ukayzm/dwr/proto1/test/motor_direction/README.md

# Test Motor Direction

It loops with these actions:
* Two motors rotate forward for 1 second in max speed
* Two motors pause for 1 second
* Two motors rotate backward for 1 second in max speed
* Two motors stop for 3 second

The followings can be tested:
* wire connections
* direction of motor and wheel. Switch dirA and dirB if the rotation direction is in reverse.
