ukayzm/dwr/proto1/sketch/motor.h

#ifndef __MOTOR_H__
#define __MOTOR_H__


#include <inttypes.h>


class Motor
{
public:
	void setRpm(int16_t rpm) {
		tgtRpm = rpm;
	}
	int16_t getAccelRpm(void) {
		return curRpm - prevRpm;
	}
	int16_t getCurRpm(void) {
		return curRpm;
	}
	int16_t getMaxRpm(void) {
		return maxRpm;
	}
	void incRpmPercent(int percent_point)
	{
		int16_t new_rpm = tgtRpm + (long)maxRpm * percent_point / 100;
		if (new_rpm >= maxRpm) {
			new_rpm = maxRpm;
		} else if (new_rpm <= -maxRpm) {
			new_rpm = -maxRpm;
		}
		setRpm(new_rpm);
	}
	virtual void loop(void);
	int id;
protected:
	int16_t maxRpm, tgtRpm;
	int16_t prevRpm, curRpm;
};


#endif // __MOTOR_H__
