ukayzm/dwr/tests/hc05_data/hc05_data.ino

#include <SoftwareSerial.h>

SoftwareSerial BTserial(A0, A1); // RX | TX
const long baudRate = 115200;

#define MAX_CHAR	128
char line_buf[MAX_CHAR];
int buf_len = 0;

void setup() 
{
	Serial.begin(115200);
	Serial.print("Sketch:   ");   Serial.println(__FILE__);
	Serial.print("Uploaded: ");   Serial.println(__DATE__);

	BTserial.begin(baudRate);  
	Serial.print("BTserial started at "); Serial.println(baudRate);
	Serial.print("> ");
}

void loop()
{
	// Read from the Bluetooth module and send to the Arduino Serial Monitor
	if (BTserial.available()) {
		char c = BTserial.read();
		Serial.write(c);
		if (c == '\n') {
			Serial.write("> ");
		}
	}

	// Read from the Serial Monitor and send to the Bluetooth module
	if (Serial.available()) {
		char c = Serial.read();
		if (buf_len < MAX_CHAR) {
			line_buf[buf_len++] = c;
		}
		Serial.write(c);
		if (buf_len == MAX_CHAR || c == '\n') {
			unsigned long start_usec = micros();
			for (int i = 0; i < buf_len; i++) {
				BTserial.write(line_buf[i]);   
			}
			unsigned long cur_usec = micros();
			Serial.print(buf_len);
			Serial.print(F(" chars sent in "));
			Serial.print(cur_usec - start_usec);
			Serial.println(F(" usec"));
			buf_len = 0;
		}
	}
}
