ukayzm/dwr/proto3/test/dc-motor/main/motor_test.h

#ifndef __MOTOR_TEST_H__
#define __MOTOR_TEST_H__

#include "motor.h"

extern void do_motor_test1(Motor *m0, Motor *m1);
extern void do_motor_test_pwm(Motor *m0, Motor *m1);
extern void do_motor_test2(Motor *m0, Motor *m1);
extern void do_motor_test3(Motor *m0, Motor *m1);
extern void do_motor_test4(Motor *m);

#endif // __MOTOR_TEST_H__
