ukayzm/dwr/proto1/test/mpu6050/mpu6050_dmp6.cpp

/*
 * This code is taken from https://github.com/jrowberg/i2cdevlib.
 * DMP is used without interrupt.
 */

// I2C device class (I2Cdev) demonstration Arduino sketch for MPU6050 class using DMP (MotionApps v2.0)
// 6/21/2012 by Jeff Rowberg <jeff@rowberg.net>
// Updates should (hopefully) always be available at https://github.com/jrowberg/i2cdevlib
//

/* ============================================
I2Cdev device library code is placed under the MIT license
Copyright (c) 2012 Jeff Rowberg

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
THE SOFTWARE IS PROVIDED "AS IS", WITHOUT WARRANTY OF ANY KIND, EXPRESS OR
IMPLIED, INCLUDING BUT NOT LIMITED TO THE WARRANTIES OF MERCHANTABILITY,
FITNESS FOR A PARTICULAR PURPOSE AND NONINFRINGEMENT. IN NO EVENT SHALL THE
AUTHORS OR COPYRIGHT HOLDERS BE LIABLE FOR ANY CLAIM, DAMAGES OR OTHER
LIABILITY, WHETHER IN AN ACTION OF CONTRACT, TORT OR OTHERWISE, ARISING FROM,
OUT OF OR IN CONNECTION WITH THE SOFTWARE OR THE USE OR OTHER DEALINGS IN
THE SOFTWARE.
===============================================
*/

// I2Cdev and MPU6050 must be installed as libraries, or else the .cpp/.h files
// for both classes must be in the include path of your project
#include "I2Cdev.h"

#include "MPU6050_6Axis_MotionApps20.h"
//#include "MPU6050.h" // not necessary if using MotionApps include file

// Arduino Wire library is required if I2Cdev I2CDEV_ARDUINO_WIRE implementation
// is used in I2Cdev.h
#if I2CDEV_IMPLEMENTATION == I2CDEV_ARDUINO_WIRE
    #include "Wire.h"
#endif

#include "mpu6050_dmp6.h"


// class default I2C address is 0x68
// specific I2C addresses may be passed as a parameter here
// AD0 low = 0x68 (default for SparkFun breakout and InvenSense evaluation board)
// AD0 high = 0x69
MPU6050 mpu;
//MPU6050 mpu(0x69); // <-- use for AD0 high

/* =========================================================================
   NOTE: In addition to connection 3.3v, GND, SDA, and SCL, this sketch
   depends on the MPU-6050's INT pin being connected to the Arduino's
   external interrupt #0 pin. On the Arduino Uno and Mega 2560, this is
   digital I/O pin 2.
 * ========================================================================= */

/* =========================================================================
   NOTE: Arduino v1.0.1 with the Leonardo board generates a compile error
   when using Serial.write(buf, len). The Teapot output uses this method.
   The solution requires a modification to the Arduino USBAPI.h file, which
   is fortunately simple, but annoying. This will be fixed in the next IDE
   release. For more info, see these links:

   http://arduino.cc/forum/index.php/topic,109987.0.html
   http://code.google.com/p/arduino/issues/detail?id=958
 * ========================================================================= */


// orientation/motion vars
float euler[3];         // [psi, theta, phi]    Euler angle container
float ypr[3];           // [yaw, pitch, roll]   yaw/pitch/roll container and gravity vector


// ================================================================
// ===                      INITIAL SETUP                       ===
// ================================================================

void setup_mpu6050_dmp6() {
    // join I2C bus (I2Cdev library doesn't do this automatically)
    #if I2CDEV_IMPLEMENTATION == I2CDEV_ARDUINO_WIRE
        Wire.begin();
        Wire.setClock(400000); // 400kHz I2C clock. Comment this line if having compilation difficulties
    #elif I2CDEV_IMPLEMENTATION == I2CDEV_BUILTIN_FASTWIRE
        Fastwire::setup(400, true);
    #endif

    // NOTE: 8MHz or slower host processors, like the Teensy @ 3.3V or Arduino
    // Pro Mini running at 3.3V, cannot handle this baud rate reliably due to
    // the baud timing being too misaligned with processor ticks. You must use
    // 38400 or slower in these cases, or use some kind of external separate
    // crystal solution for the UART timer.

    // initialize device
    Serial.println(F("Init mpu"));
    mpu.initialize();

    // verify connection
	if (mpu.testConnection() == false) {
    	Serial.println(F("mpu failed"));
	}

    // load and configure the DMP
    uint8_t devStatus = mpu.dmpInitialize();

    // supply your own gyro offsets here, scaled for min sensitivity
    mpu.setXGyroOffset(220);
    mpu.setYGyroOffset(76);
    mpu.setZGyroOffset(-85);
    mpu.setZAccelOffset(1788); // 1688 factory default for my test chip

    // make sure it worked (returns 0 if so)
    if (devStatus == 0) {
        // Calibration Time: generate offsets and calibrate our MPU6050
        mpu.CalibrateAccel(6);
        mpu.CalibrateGyro(6);
        mpu.PrintActiveOffsets();
        // turn on the DMP, now that it's ready
        mpu.setDMPEnabled(true);

        // set our DMP Ready flag so the main loop() function knows it's okay to use it
        Serial.println(F("DMP ready!"));
    } else {
        // ERROR!
        // 1 = initial memory load failed
        // 2 = DMP configuration updates failed
        // (if it's going to break, usually the code will be 1)
        Serial.print(F("DMP Init failed (code "));
        Serial.print(devStatus);
        Serial.println(F(")"));
    }
}



// ================================================================
// ===                    MAIN PROGRAM LOOP                     ===
// ================================================================

int loop_mpu6050_dmp6(void) {
	uint8_t fifoBuffer[64]; // FIFO storage buffer
    // read a packet from FIFO (every 10 msec)
    if (mpu.dmpGetCurrentFIFOPacket(fifoBuffer)) { // Get the Latest packet 
		Quaternion q;           // [w, x, y, z]         quaternion container
		VectorFloat gravity;    // [x, y, z]            gravity vector
		mpu.dmpGetQuaternion(&q, fifoBuffer);
		mpu.dmpGetEuler(euler, &q);
		mpu.dmpGetGravity(&gravity, &q);
		mpu.dmpGetYawPitchRoll(ypr, &q, &gravity);

#ifdef OUTPUT_READABLE_EULER
		// display Euler angles in degrees
		Serial.print("euler\t");
		Serial.print(euler[0] * 180/M_PI);
		Serial.print("\t");
		Serial.print(euler[1] * 180/M_PI);
		Serial.print("\t");
		Serial.println(euler[2] * 180/M_PI);
#endif

#ifdef OUTPUT_READABLE_YAWPITCHROLL
		// display Euler angles in degrees
		Serial.print("ypr\t");
		Serial.print(ypr[0] * 180/M_PI);
		Serial.print("\t");
		Serial.print(ypr[1] * 180/M_PI);
		Serial.print("\t");
		Serial.println(ypr[2] * 180/M_PI);
#endif
		return 0;
    }
	return 1;
}
